Capobuf/ESP-DubSiren/firmware/src/audio/Delay.h

#pragma once

#include <stddef.h>
#include <stdint.h>

#include "Biquad.h"
#include "SmoothedParameter.h"

class Delay {
public:
    static constexpr size_t kBufferSamples = 48000;

    Delay();
    void begin(float initialDelayMs, float highPassHz, float lowPassHz,
               float sampleRate);
    void setParameters(float delayMs, float highPassHz, float lowPassHz,
                       float sampleRate);
    float process(float dry, float feedback, float sampleRate);

private:
    int16_t buffer_[kBufferSamples];
    size_t writeIndex_;
    SmoothedParameter delayMs_;
    SmoothedParameter highPassHz_;
    SmoothedParameter lowPassHz_;
    unsigned filterUpdateCountdown_;
    float appliedHighPassHz_;
    float appliedLowPassHz_;
    Biquad highPass_;
    Biquad lowPass_;
};
